ClockWorkKid/WiFi-Nano-Quadcopter/Quadcopter CAD Models/65mm-prop-1.snapshot.1/06.png

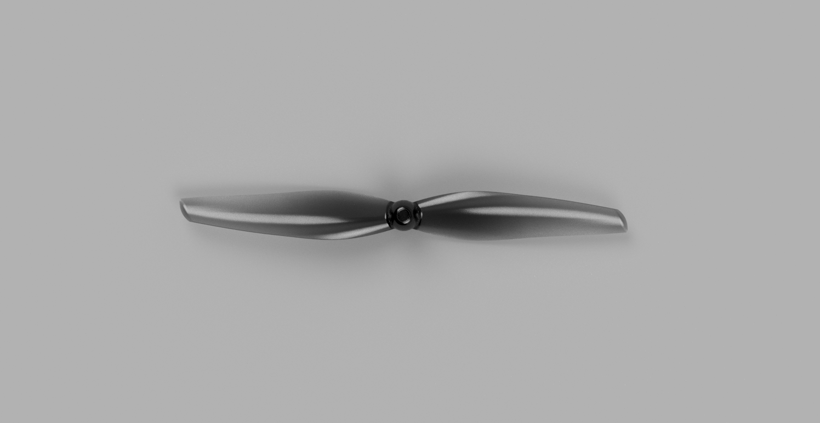
Quadcopter CAD Models/65mm-prop-1.snapshot.1/06.png
