ClockWorkKid/WiFi-Nano-Quadcopter/Quadcopter CAD Models/Micro_105_FPV_Quadcopter_-_8.5mm_Motors_Micro_Scisky/images/0fb575de4e6bde61108f173f8af68898_preview_featured.jpg

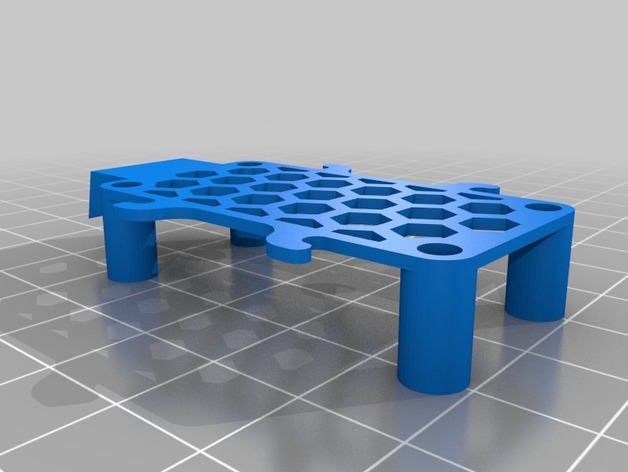
Quadcopter CAD Models/Micro_105_FPV_Quadcopter_-_8.5mm_Motors_Micro_Scisky/images/0fb575de4e6bde61108f173f8af68898_preview_featured.jpg
