ClockWorkKid/WiFi-Nano-Quadcopter/Quadcopter CAD Models/Micro_105_FPV_Quadcopter_-_8.5mm_Motors_Micro_Scisky/images/6a48a7edb29f2dee5ecd6720a6caf826_preview_featured.jpg

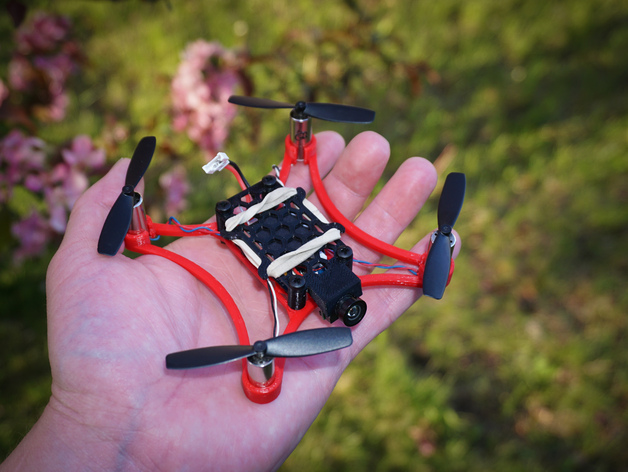
Quadcopter CAD Models/Micro_105_FPV_Quadcopter_-_8.5mm_Motors_Micro_Scisky/images/6a48a7edb29f2dee5ecd6720a6caf826_preview_featured.jpg
