ClockWorkKid/WiFi-Nano-Quadcopter/Quadcopter CAD Models/Micro_105_FPV_Quadcopter_-_8.5mm_Motors_Micro_Scisky/images/8fe7323692de997f5eb6b96ab5407ec9_preview_featured.jpg

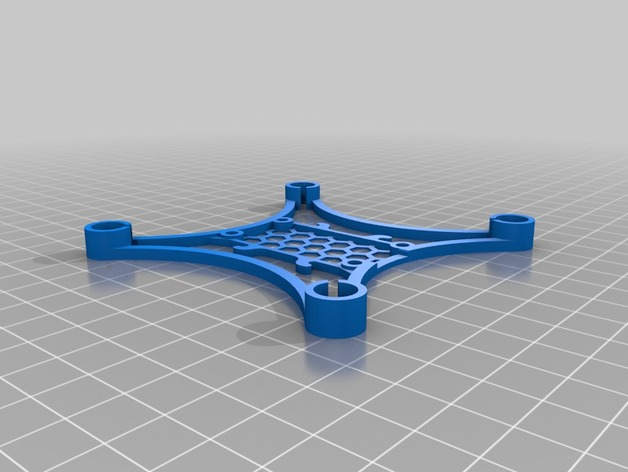
Quadcopter CAD Models/Micro_105_FPV_Quadcopter_-_8.5mm_Motors_Micro_Scisky/images/8fe7323692de997f5eb6b96ab5407ec9_preview_featured.jpg
