ClockWorkKid/WiFi-Nano-Quadcopter/Quadcopter CAD Models/Micro_105_FPV_Quadcopter_-_8.5mm_Motors_Micro_Scisky/images/84fe873a652a19607980b344e2987434_preview_featured.jpg

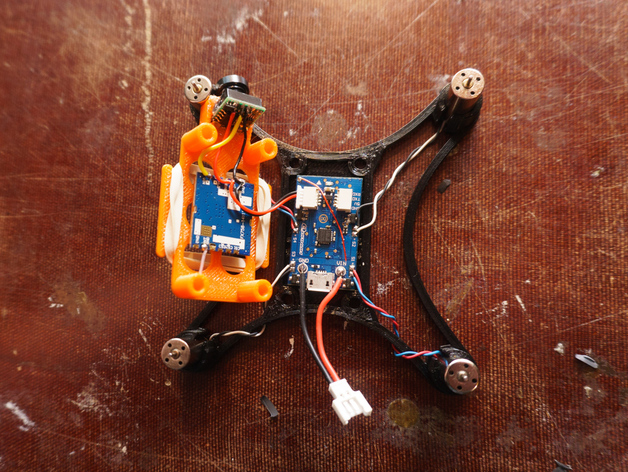
Quadcopter CAD Models/Micro_105_FPV_Quadcopter_-_8.5mm_Motors_Micro_Scisky/images/84fe873a652a19607980b344e2987434_preview_featured.jpg
