ClockWorkKid/WiFi-Nano-Quadcopter/Quadcopter CAD Models/Micro_105_FPV_Quadcopter_-_8.5mm_Motors_Micro_Scisky/images/832be2155cdcdc327818c795284aadd3_preview_featured.jpg

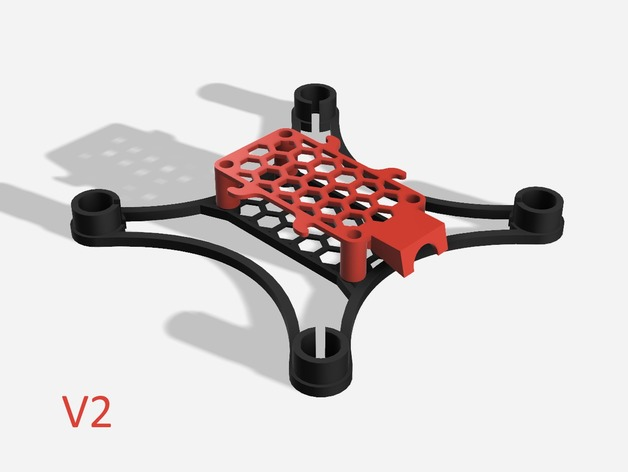
Quadcopter CAD Models/Micro_105_FPV_Quadcopter_-_8.5mm_Motors_Micro_Scisky/images/832be2155cdcdc327818c795284aadd3_preview_featured.jpg
