ClockWorkKid/WiFi-Nano-Quadcopter/Quadcopter CAD Models/Ryze_Tello_Propellers/images/2cdfefd59b9e02c92c9f1799bc0e8fc2_preview_featured.jpg

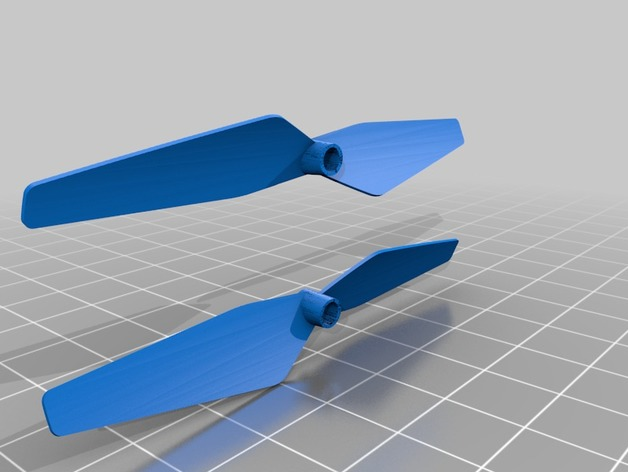
Quadcopter CAD Models/Ryze_Tello_Propellers/images/2cdfefd59b9e02c92c9f1799bc0e8fc2_preview_featured.jpg
