ClockWorkKid/WiFi-Nano-Quadcopter/Quadcopter CAD Models/Ryze_Tello_Propellers/images/3993e07cd14e0140e9b3e32e3a5cb526_preview_featured.jpg

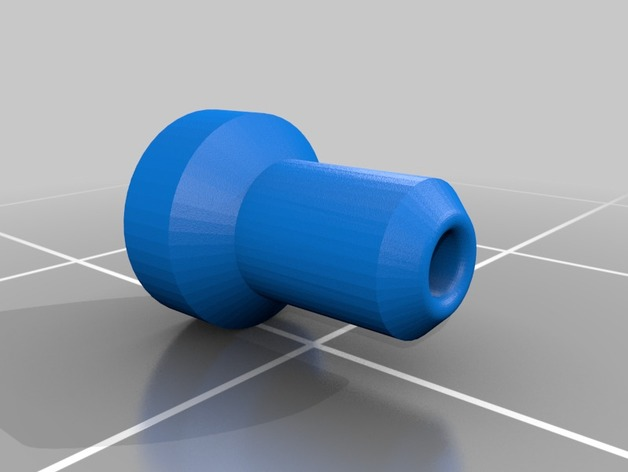
Quadcopter CAD Models/Ryze_Tello_Propellers/images/3993e07cd14e0140e9b3e32e3a5cb526_preview_featured.jpg
