ClockWorkKid/WiFi-Nano-Quadcopter/Quadcopter CAD Models/Ryze_Tello_Propellers/images/fef2fb93c76f4957c0f6beac872d470d_preview_featured.jpg

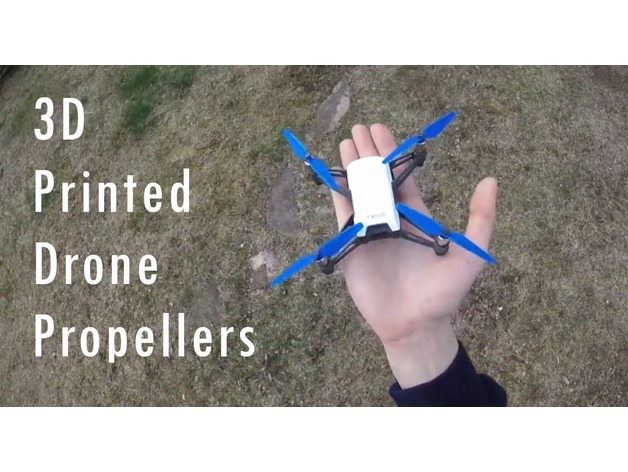
Quadcopter CAD Models/Ryze_Tello_Propellers/images/fef2fb93c76f4957c0f6beac872d470d_preview_featured.jpg
