ClockWorkKid/WiFi-Nano-Quadcopter/Quadcopter CAD Models/Micro_105_FPV_Quadcopter_-_8.5mm_Motors_Micro_Scisky/files/micro105-bottom-v4-bottom-battery.stl

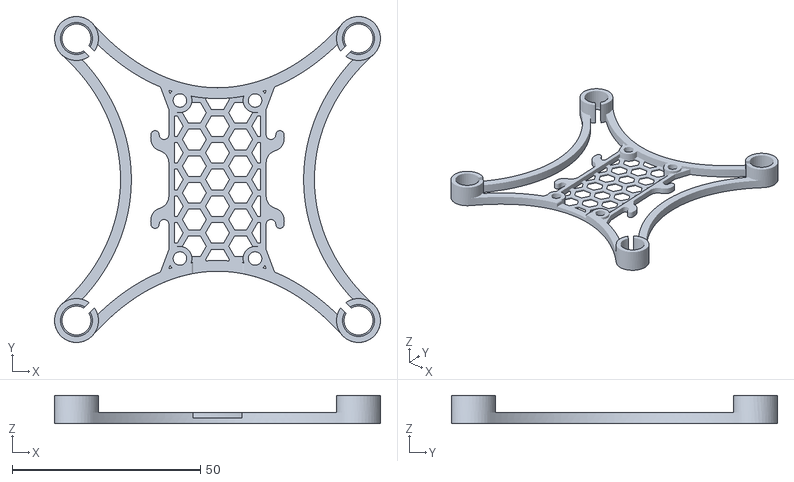
[picture p39: CAD file, 2020-05-22]
Quadcopter CAD Models/Micro_105_FPV_Quadcopter_-_8.5mm_Motors_Micro_Scisky/files/micro105-bottom-v4-bottom-battery.stl
86.7 x 86.7 x 7.50
