ClockWorkKid/WiFi-Nano-Quadcopter/Quadcopter CAD Models/Tello-STL-Files/Coreless_Motor.SLDPRT

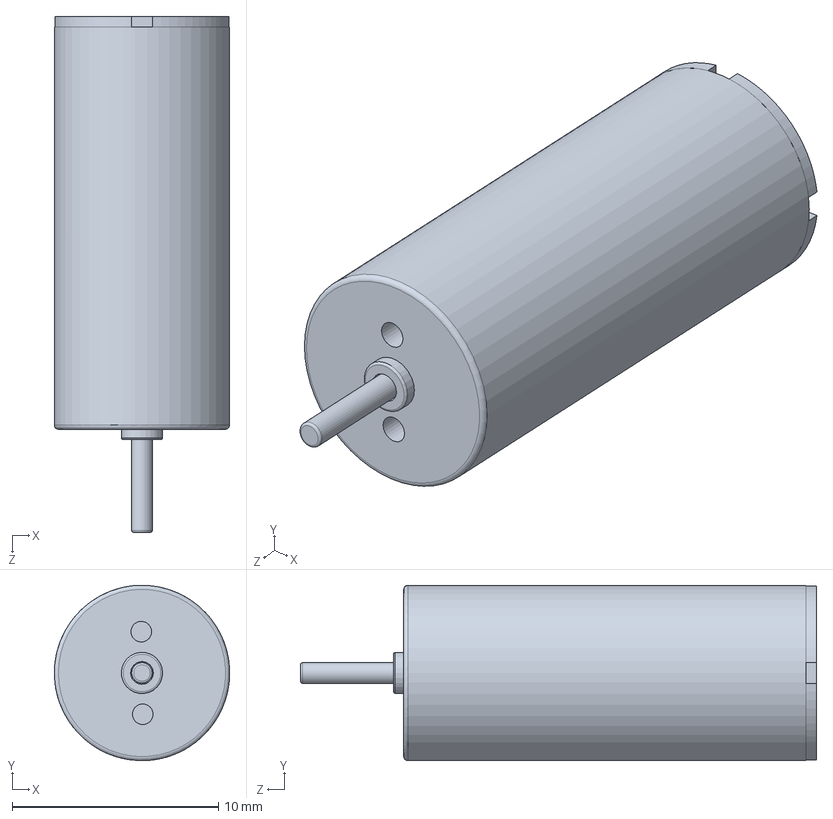
[picture p40: CAD file, 2020-05-22]
Quadcopter CAD Models/Tello-STL-Files/Coreless_Motor.SLDPRT
8.50 x 8.49 x 25.0 mm
