ClockWorkKid/WiFi-Nano-Quadcopter/Quadcopter CAD Models/Micro_105_FPV_Quadcopter_-_8.5mm_Motors_Micro_Scisky/files/micro105-top-v2-no-cam.stl

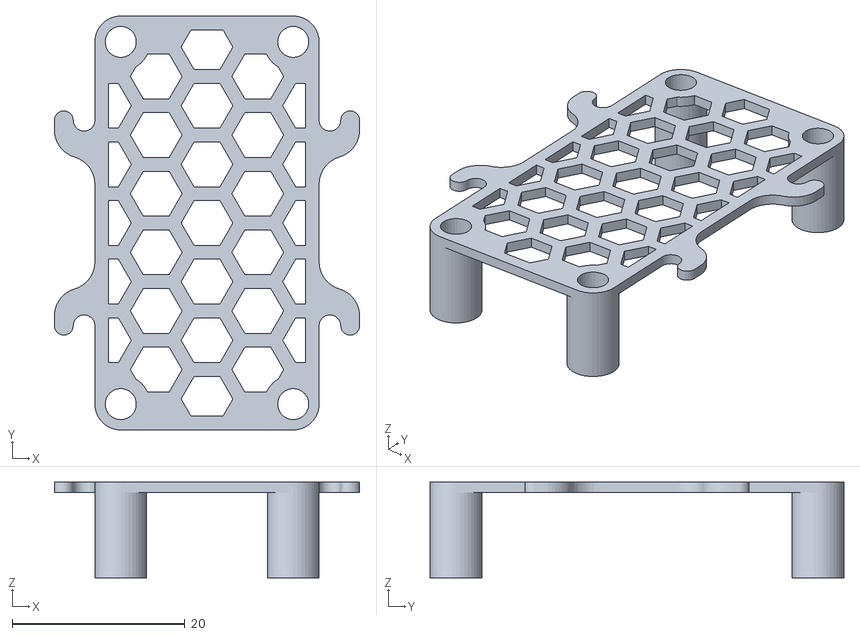
[picture p41: CAD file, 2020-05-22]
Quadcopter CAD Models/Micro_105_FPV_Quadcopter_-_8.5mm_Motors_Micro_Scisky/files/micro105-top-v2-no-cam.stl
35.4 x 48.0 x 11.1
