ClockWorkKid/WiFi-Nano-Quadcopter/Quadcopter CAD Models/Micro_105_FPV_Quadcopter_-_8.5mm_Motors_Micro_Scisky/files/micro105-top-v1.stl

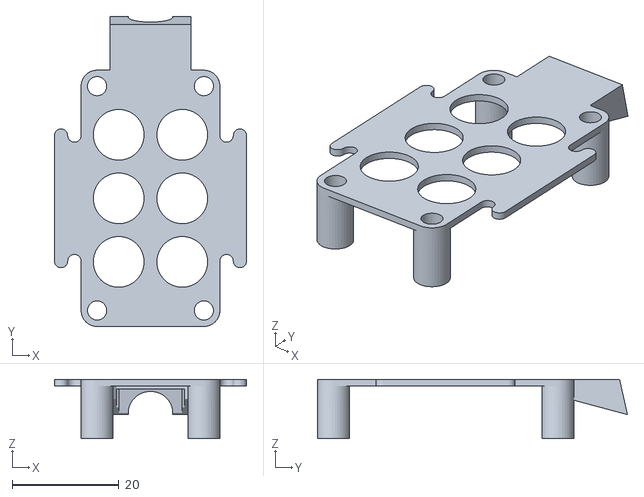
[picture p43: CAD file, 2020-05-22]
Quadcopter CAD Models/Micro_105_FPV_Quadcopter_-_8.5mm_Motors_Micro_Scisky/files/micro105-top-v1.stl
36.0 x 58.0 x 11.1
