ClockWorkKid/WiFi-Nano-Quadcopter/Quadcopter CAD Models/Micro_105_FPV_Quadcopter_-_8.5mm_Motors_Micro_Scisky/files/micro105-bottom-v4-7mm-bottom-battery.stl

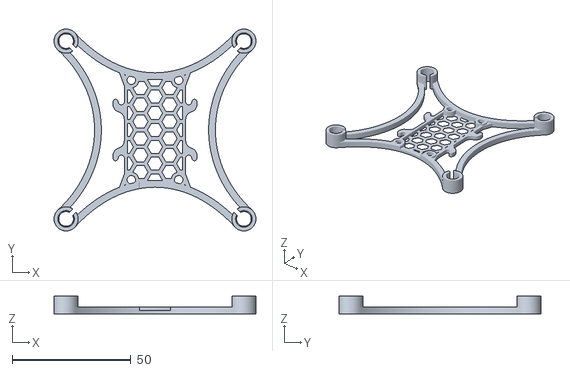
[picture p44: CAD file, 2020-05-22]
Quadcopter CAD Models/Micro_105_FPV_Quadcopter_-_8.5mm_Motors_Micro_Scisky/files/micro105-bottom-v4-7mm-bottom-battery.stl
85.2 x 85.2 x 7.50
