ClockWorkKid/WiFi-Nano-Quadcopter/Tests/Build 0/NodeMCU_V2_v2.png

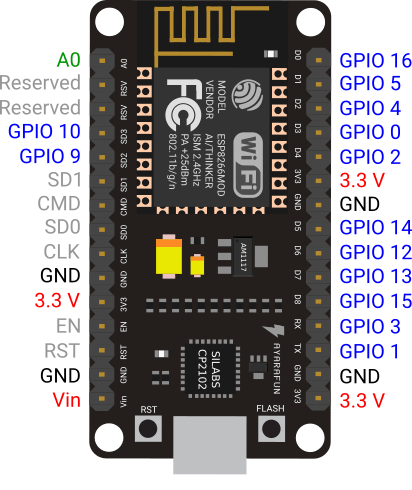
Tests/Build 0/NodeMCU_V2_v2.png
