ClockWorkKid/WiFi-Nano-Quadcopter/Tests/ESP-Quadcopter-Codes/ESPCOPTER_original/ESPcopter 1.0.3_2 BETA/espcopter/examples/Espcopter/Espcopter/data/media/info.png

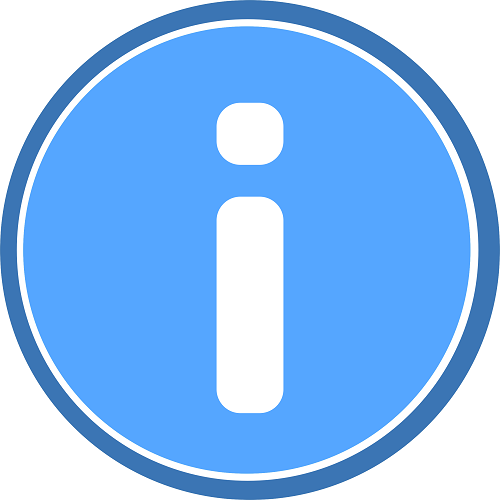
Tests/ESP-Quadcopter-Codes/ESPCOPTER_original/ESPcopter 1.0.3_2 BETA/espcopter/examples/Espcopter/Espcopter/data/media/info.png
