ClockWorkKid/WiFi-Nano-Quadcopter/Tests/ESP-Quadcopter-Codes/ESPCOPTER_original/ESPcopter 1.0.3_2 BETA/espcopter/examples/modules/alttidueHold/GetData/GetData.ino

/*
 * www.espcopter.com/learn
 * 
*/
#define standalone

#include <espcopter.h> // ESPcopter kütüphanesi


void setup() {
  mainSetup(); // uçuş ayarları
 }

void loop() {
   mainLoop ();  // uçuş kontrol döngüsü
   Serial.print("Yukseklik: ");
   Serial.print(getMeasureAltitude());
   Serial.println("mm");
}
