ClockWorkKid/WiFi-Nano-Quadcopter/Tests/ESP-Quadcopter-Codes/ESPCOPTER_original/ESPcopter 1.0.3_2 BETA/espcopter/examples/modules/buzzer/HappyBirthDay/HappyBirthDay.ino

/*
 * www.espcopter.com/learn
 * 
*/
// * Happy Birthday to You

int length = 28; 
char notes[] = "GGAGcB GGAGdc GGxecBA yyecdc";
int beats[] = { 2, 2, 8, 8, 8, 16, 1, 2, 2, 8, 8,8, 16, 1, 2,2,8,8,8,8,16, 1,2,2,8,8,8,16 };
int tempo = 150;

void playTone(int tone, int duration) {
for (long i = 0; i < duration * 1000L; i += tone * 2) {
 analogWrite(2, 0);
 analogWrite(12, 40);
 analogWrite(13, 40);
 analogWrite(14, 40);
 analogWrite(15, 40);    
 delayMicroseconds(tone);
 analogWrite(2, 1023);
 analogWrite(12, 0);
 analogWrite(13, 0);
 analogWrite(14, 0);
 analogWrite(15, 0);
 delayMicroseconds(tone);
}
}

void playNote(char note, int duration) {

char names[] = {'C', 'D', 'E', 'F', 'G', 'A', 'B',           

                 'c', 'd', 'e', 'f', 'g', 'a', 'b',

                 'x', 'y' };

int tones[] = { 1915, 1700, 1519, 1432, 1275, 1136, 1014,

                 956,  834,  765,  593,  468,  346,  224,

                 655 , 715 };

int SPEE = 5;
// play the tone corresponding to the note name
for (int i = 0; i < 17; i++) {
   if (names[i] == note) {
    int newduration = duration/SPEE;
     playTone(tones[i], newduration);

   }
}
}

void setup() {
pinMode(2, OUTPUT);
}

void loop() {
for (int i = 0; i < length; i++) {
   if (notes[i] == ' ') {
     delay(beats[i] * tempo); // rest
   } else {
     playNote(notes[i], beats[i] * tempo);
   }
 analogWrite(16, 1000);
   // pause between notes
   delay(tempo);
 analogWrite(16, 0);
}
}
