ClockWorkKid/WiFi-Nano-Quadcopter/Tests/Codes-Test/SONAR/IR_Receiver/interrupt_recv.ino

//int counter = 0;
//
//#define sync1 4 //D2
////#define sync1 5 //D1
//
//void setup() {
//  Serial.begin(115200);
//  attachInterrupt(digitalPinToInterrupt(sync1), pulseCB, FALLING);
//}
//
//ICACHE_RAM_ATTR void pulseCB() {
//  counter++;
//  Serial.println(counter);
//}
//
//
//void loop() {
//
//}
