ClockWorkKid/WiFi-Nano-Quadcopter/Tests/Codes-Test/SONAR/IR_Receiver/remote_recv.ino

#include <Arduino.h>
#include <IRremoteESP8266.h>
#include <IRrecv.h>
#include <IRutils.h>

// An IR detector/demodulator is connected to GPIO pin 14(D5 on a NodeMCU
// board).
// Note: GPIO 16 won't work on the ESP8266 as it does not have interrupts.
const uint16_t kRecvPin = 14;

IRrecv irrecv(kRecvPin);

decode_results results;

void setup() {
  Serial.begin(115200);
  irrecv.enableIRIn();  // Start the receiver

  Serial.println();
  Serial.print("IRrecvDemo is now running and waiting for IR message on Pin ");
  Serial.println(kRecvPin);
}

unsigned long counter=0;

void loop() {
  if (irrecv.decode(&results)) {
    Serial.print(counter++);
    Serial.print(" ");
    serialPrintUint64(results.value);
    Serial.println("");
    irrecv.resume();  // Receive the next value
  }
}
