ClockWorkKid/WiFi-Nano-Quadcopter/Tests/Codes-Test/SONAR/IR_Transmitter/remote_tran.ino

/*
 * IRremote: IRsendDemo - demonstrates sending IR codes with IRsend
 * An IR LED must be connected to Arduino PWM pin 3.
 * Version 0.1 July, 2009
 * Copyright 2009 Ken Shirriff
 * http://arcfn.com
 */

#include <IRremote.h>

IRsend IrSender;

// On the Zero and others we switch explicitly to SerialUSB
#if defined(ARDUINO_ARCH_SAMD)
#define Serial SerialUSB
#endif

void setup() {
    pinMode(LED_BUILTIN, OUTPUT);

    Serial.begin(115200);
#if defined(__AVR_ATmega32U4__) || defined(SERIAL_USB) || defined(SERIAL_PORT_USBVIRTUAL)
    delay(2000); // To be able to connect Serial monitor after reset and before first printout
#endif
    // Just to know which program is running on my Arduino
    Serial.println(F("START " __FILE__ " from " __DATE__));
    Serial.print(F("Ready to send IR signals at pin "));
    Serial.println(IR_SEND_PIN);
}

unsigned long counter=0;

void loop() {
    unsigned long tData = 0xb91;
    IrSender.sendSony(tData, 12);
    Serial.print(counter++);
    Serial.print(" ");
    Serial.println(tData);
//        IrSender.sendJVC(0xC5B8, 16,0); // hex value, 16 bits, no repeat
//        delayMicroseconds(50); // see http://www.sbprojects.com/knowledge/ir/jvc.php for information
//        IrSender.sendJVC(0xC5B8, 16,1); // hex value, 16 bits, repeat
//        Serial.println(F("sendJVC(9xC5B8, 16)"));

    delay(1000); //5 second delay between each signal burst
}
