ClockWorkKid/WiFi-Nano-Quadcopter/Tests/Codes-Test/SONAR/IR_Transmitter/timer.ino

//unsigned long timer = 0;
//bool state = 0;
//
//void setup() {
//  pinMode(13, OUTPUT);
//
//  TCCR0A = (1 << WGM01); //Set the CTC mode
//  OCR0A = 1;          //Value for ORC0A for 1ms
//
//  TIMSK0 |= (1 << OCIE0A); //Set the interrupt request
//  sei(); //Enable interrupt
//
//  TCCR0B |= (1 << CS01); //Set the prescale 1/64 clock
//  TCCR0B |= (1 << CS00);
//
//}
//
//void loop() {
//
//}
//
//ISR(TIMER0_COMPA_vect) {   //This is the interrupt request
//  timer++;
//  //in this way you can count 1 second because the nterrupt request is each 1ms
//  if (timer >= 125000) {
//    state = !state;
//    timer = 0;
//    digitalWrite(13, state);
//  }
//
//}
