ClockWorkKid/WiFi-Nano-Quadcopter/Tests/ESP-Quadcopter-Codes/ESPCOPTER_original/ESPcopter 1.0.3_2 BETA/espcopter/src/AHRS.cpp

#include "AHRS.h"
#include <Wire.h>


int previousDegree;
 float angle=0;
 float heading=0;


String AHRS::setupOutput(){

  String ahrsOutput= "";
  
  ahrsOutput = ahrsOutput + "-----------------------------"  + '\n';
  ahrsOutput = ahrsOutput + "Calibration Data:"  + '\n';
  ahrsOutput = ahrsOutput + "Magnometer Motor Calibraiton: " + '\n';
  ahrsOutput = ahrsOutput + "MagX: "  ;
  ahrsOutput = ahrsOutput + magOffsetMotorEpr[0];
  ahrsOutput = ahrsOutput +" MagY: ";
  ahrsOutput = ahrsOutput + magOffsetMotorEpr[1] + '\n';
      
  ahrsOutput = ahrsOutput + "-----------------------------"  + '\n';
  ahrsOutput = ahrsOutput + "Magnometer Calibraiton: "  + '\n';
  ahrsOutput = ahrsOutput + "Offx: ";
  ahrsOutput = ahrsOutput + magOffset[0];
  ahrsOutput = ahrsOutput + " Offy: ";
  ahrsOutput = ahrsOutput + magOffset[1];
  ahrsOutput = ahrsOutput + " Offz: ";
  ahrsOutput = ahrsOutput + magOffset[2] + '\n';

  ahrsOutput = ahrsOutput + "-----------------------------"  + '\n';
  ahrsOutput = ahrsOutput + "GYRO Calibration: "  + '\n'; 
  ahrsOutput = ahrsOutput + "GYROX: ";
  ahrsOutput = ahrsOutput + MEAN_GYRO[0];
  ahrsOutput = ahrsOutput + " GYROY: ";
  ahrsOutput = ahrsOutput + MEAN_GYRO[1];
  ahrsOutput = ahrsOutput + " GYROZ: ";
  ahrsOutput = ahrsOutput + MEAN_GYRO[2] + '\n';

  I2Cread(MPU9250_ADDRESS,0x3B,14,Buf);
  accel[0]=(Buf[0]<<8 | Buf[1]) - MEAN_ACCE[0]; 
  accel[1]=(Buf[2]<<8 | Buf[3]) - MEAN_ACCE[1]; 
  accel[2]=(Buf[4]<<8 | Buf[5]) - MEAN_ACCE[2];
 
  // Gyroscope
  gyro_int[0]=(Buf[8]<<8 | Buf[9]) - MEAN_GYRO[0];
  gyro_int[1]=(Buf[10]<<8 | Buf[11]) - MEAN_GYRO[1];
  gyro_int[2]=Buf[12]<<8 | Buf[13] - MEAN_GYRO[2];


  ahrsOutput = ahrsOutput + "-----------------------------"  + '\n';
  ahrsOutput = ahrsOutput + "GYRO Data: "  + '\n'; 
  ahrsOutput = ahrsOutput + "GYRO_Roll: ";
  ahrsOutput = ahrsOutput + gyro_int[0];
  ahrsOutput = ahrsOutput + " GYRO_Pitch: ";
  ahrsOutput = ahrsOutput + gyro_int[1];
  ahrsOutput = ahrsOutput + " GYRO_Yaw: ";
  ahrsOutput = ahrsOutput + gyro_int[2] + '\n';

   
  ahrsOutput = ahrsOutput + "-----------------------------"  + '\n';
  ahrsOutput = ahrsOutput + "IMU Calibration: "  + '\n'; 
  ahrsOutput = ahrsOutput + "IMU_Roll: ";
  ahrsOutput = ahrsOutput + MEAN_ACCE[0];
  ahrsOutput = ahrsOutput + " IMU_Pitch: ";
  ahrsOutput = ahrsOutput + MEAN_ACCE[1] ;
  ahrsOutput = ahrsOutput + " IMU_Yaw: ";
  ahrsOutput = ahrsOutput + MEAN_ACCE[2] + '\n';
     


  ahrsOutput = ahrsOutput + "-----------------------------"  + '\n';
  ahrsOutput = ahrsOutput + "IMU Data: "  + '\n'; 
  ahrsOutput = ahrsOutput + "IMU_Roll: ";
  ahrsOutput = ahrsOutput + accel[0];
  ahrsOutput = ahrsOutput + " IMU_Pitch: ";
  ahrsOutput = ahrsOutput + accel[1];
  ahrsOutput = ahrsOutput + " IMU_Yaw: ";
  ahrsOutput = ahrsOutput + accel[2] + '\n';

 // Serial.print(ahrsOutput);
  return ahrsOutput;
}


void AHRS::calibraiton(int calMethod){
  
    Serial.print(" calMethod");
    Serial.println(calMethod);

    
   if( calMethod == 0){
   digitalWrite(redLed, 1); //  0 == 1 
   digitalWrite(greenLed, 0); // 0 == 0 
   digitalWrite(blueLed, 0); //  0 == 1

   Serial.println(" Gyro Calibration Progress Started");
   gyroCorrection(2000);

   Serial.println(" Accel Calibration Progress Started");
   accelCorrection(2000);

   digitalWrite(redLed, 1); //  0 == 1 
   digitalWrite(greenLed, 1); // 0 == 0 
   digitalWrite(blueLed, 1); //  0 == 1
   }


   if( calMethod == 1){
   digitalWrite(redLed, 1); //  0 == 1 
   digitalWrite(greenLed, 0); // 0 == 0 
   digitalWrite(blueLed, 0); //  0 == 1

   Serial.println(" Mag Calibration Progress Started");
   analogWriteFreq(20000);
   magCalStage = 1;
   magCorrection(1000);
   magCalStage =0;
   
   digitalWrite(redLed, 1); //  0 == 1 
   digitalWrite(greenLed, 1); // 0 == 0 
   digitalWrite(blueLed, 1); //  0 == 1
   }
   
   if( calMethod == 2){
  
   }
    

   

   EEPROM.write(25,highByte(0)); // aotu set 
   EEPROM.write(26,lowByte(0));
   /*
   EEPROM.write(35,highByte(0));
   EEPROM.write(36,lowByte(0));  // optical

   EEPROM.write(37,highByte(0));
   EEPROM.write(38,lowByte(0));*/                                                                

   EEPROM.write(42,highByte(0)); // yaw
   EEPROM.write(43,lowByte(0));
   
   
  EEPROM.commit();

  if( calMethod == 1){
  delay(100);
  ESP.restart();
   }
   
  
}


 
void AHRS::Initialize(){
  // Start I2C Communication
  //Wire.begin();
  Wire.setClock(400000L);
  //Wire.setClockStretchLimit(500L);
  
  // Set accelerometers low pass filter at 5Hz
  writeBIT(29, 0x06,MPU9250_ADDRESS);
  // Set gyroscope low pass filter at 5Hz
  writeBIT(26, 0x06,MPU9250_ADDRESS);
  // Configure gyroscope range
  writeBIT(27, GYRO_FULL_SCALE_2000_DPS,MPU9250_ADDRESS);
  // Configure accelerometers range
  writeBIT(28, ACC_FULL_SCALE_2_G,MPU9250_ADDRESS);
  // Set by pass mode for the magnetometers
  writeBIT(0x37, 0x02,MPU9250_ADDRESS);
  // Request continuous magnetometer measurements in 16 bits
  //writeBIT(0x0A, 0x16,MAG_ADDRESS);
   delay(20);

  writeBIT(0x0A, 0x00 , MAG_ADDRESS); // Power down magnetometer  
  delay(20);
  writeBIT(0x0A  , 0x0F, MAG_ADDRESS); // Enter Fuse ROM access mode
  delay(20);
  uint8_t rawData[3];
  I2Cread(MAG_ADDRESS,0x10,3,rawData);
  destination[0] =  (float)(rawData[0] - 128)/256. + 1.;   // Return x-axis sensitivity adjustment values, etc.
  destination[1] =  (float)(rawData[1] - 128)/256. + 1.;  
  destination[2] =  (float)(rawData[2] - 128)/256. + 1.; //28 , 238 , 254 , 0.61 , 1.43 , 1.49

   Serial.print("Sensitivity: ");
   Serial.print(destination[0]);
   Serial.print(" , ");
   Serial.print(destination[1]);
   Serial.print(" , ");
   Serial.println(destination[2]);
   delay(20);
   
   writeBIT(0x0A, 0x00, MAG_ADDRESS); // Power down magnetometer  
   delay(20);
   // Configure the magnetometer for continuous read and highest resolution
   // set Mscale bit 4 to 1 (0) to enable 16 (14) bit resolution in CNTL register,
   // and enable continuous mode data acquisition Mmode (bits [3:0]), 0010 for 8 Hz and 0110 for 100 Hz sample rates
   writeBIT(0x0A, Mscale << 4 | Mmode,MAG_ADDRESS); // Set magnetometer data resolution and sample ODR
   delay(20);
 
  
  
   Serial.print("Read Eeprom...");


   MEAN_GYRO[0] = word(EEPROM.read(1),EEPROM.read(2));
   MEAN_GYRO[1] = word(EEPROM.read(3),EEPROM.read(4));
   MEAN_GYRO[2] = word(EEPROM.read(5),EEPROM.read(6));


   MEAN_ACCE[0] = word(EEPROM.read(70),EEPROM.read(71));
   MEAN_ACCE[1] = word(EEPROM.read(72),EEPROM.read(73));
   MEAN_ACCE[2] = word(EEPROM.read(74),EEPROM.read(75));

   magOffset[0] = word(EEPROM.read(10),EEPROM.read(11));
   magOffset[1] = word(EEPROM.read(20),EEPROM.read(21));
   magOffset[2] = word(EEPROM.read(30),EEPROM.read(31));

   magOffsetMotorEpr[0] = word(EEPROM.read(40),EEPROM.read(41));
   magOffsetMotorEpr[1] = word(EEPROM.read(50),EEPROM.read(51));
 
   magOffsetMotorEpr[2] = word(EEPROM.read(45),EEPROM.read(46));
   magOffsetMotorEpr[3] = word(EEPROM.read(55),EEPROM.read(56));

  // destination2[0] = word(EEPROM.read(12),EEPROM.read(13))/100;
  // destination2[1] = word(EEPROM.read(14),EEPROM.read(15))/100;



    
  Serial.print(" destination20: ");
  Serial.print(destination2[0]);
  Serial.print(" destination21: ");
  Serial.print(destination2[1]);
  Serial.print(" MagX: ");
  Serial.print(magOffsetMotorEpr[0]);
  Serial.print(" MagY: ");
  Serial.print(magOffsetMotorEpr[1]);
  Serial.print(" Offx: ");
  Serial.print(magOffset[0]);
  Serial.print(" Offy: ");
  Serial.print(magOffset[1]);
  Serial.print(" Offz:");
  Serial.print(magOffset[2]);  
  Serial.print(" GYROX: "); 
  Serial.print(MEAN_GYRO[0]);
  Serial.print(" GYROY: ");
  Serial.print(MEAN_GYRO[1]);
  Serial.print(" GYROZ: ");
  Serial.println(MEAN_GYRO[2]);
}

void AHRS::writeBIT(int addr, int data, int adrrTrans){
  Wire.beginTransmission(adrrTrans);
  Wire.write(addr);
  Wire.write(data);
  Wire.endTransmission();
}
void AHRS::I2Cread(uint8_t Address, uint8_t Register, uint8_t Nbytes, uint8_t* Data){
// Set register address
Wire.beginTransmission(Address);
Wire.write(Register);
Wire.endTransmission();
// Read Nbytes
Wire.requestFrom(Address, Nbytes); 
uint8_t index=0;
while (Wire.available())
Data[index++]=Wire.read();
}

float AHRS::rad2deg(float rad){
  float output = rad * (180.0 / PI);
  return output;
}

float AHRS::deg2rad(float deg){
  float output = deg * (PI / 180.0);
  return output;
}

void AHRS::setTrimRoll(int16_t trimRoll_){
   trimRoll =  trimRoll_;
}
void AHRS::setTrimPitch(int16_t trimPitch_){
   trimPitch =  trimPitch_;
}

float AHRS::getAccelX(){
  return accel[0];
}

float AHRS::getAccelY(){
  return accel[1];
}

float AHRS::getAccelZ(){
  return accel[2];
}

float AHRS::getGyroX(){
  return gyro_int[0];
}

float AHRS::getGyroY(){
  return gyro_int[1];
}
float AHRS::getGyroZ(){
  return gyro_int[2];
}

void AHRS::compute(float attitude[3], float rate[3],float attitudeRadian[3], float rateRadian[3] ){
    timenow = millis();
    dt = (float)(timenow - timeprev)/978.;
    timeprev = timenow;

    if(dt > -1){
        
    // Get Raw Data From IMU
    I2Cread(MPU9250_ADDRESS,0x3B,14,Buf);
    accel[0]=(Buf[0]<<8 | Buf[1]) - MEAN_ACCE[0]; //-520
    accel[1]=(Buf[2]<<8 | Buf[3]) - MEAN_ACCE[1]; //-300
    accel[2]=(Buf[4]<<8 | Buf[5]) - MEAN_ACCE[2];
 
    // Gyroscope
    gyro_int[0]=(Buf[8]<<8 | Buf[9]) - MEAN_GYRO[0];
    gyro_int[1]=(Buf[10]<<8 | Buf[11]) - MEAN_GYRO[1];
    gyro_int[2]=Buf[12]<<8 | Buf[13] - MEAN_GYRO[2];

 /*
    Serial.print( gyro_int[0] );
    Serial.print(" , ");
    Serial.print( gyro_int[1] );
    Serial.print(" , ");
    Serial.print( gyro_int[2] );
    Serial.print(" , ");
    Serial.print( accel[0] );
    Serial.print(" , ");
    Serial.print( accel[1] );
    Serial.print(" , ");
    Serial.print( accel[2] );
    Serial.println(); */

      
    // Get Gyro 
    for(i = 0; i<3 ; i++){
    gyro[i] = (gyro_int[i] / GYRO_LSB)*DEG2RAD;
    }   
  
    // Normalize Accelerometer
    normalize(accel_angle, accel);
    
   // Calculate deltaAngle
    gyro_angle_x = gyro_angle_x + (gyro_angle_y* gyro[2] - gyro_angle_z* gyro[1])*dt;
    gyro_angle_y = gyro_angle_y + (gyro_angle_z* gyro[0] - gyro_angle_x* gyro[2])*dt;
    gyro_angle_z = gyro_angle_z + (gyro_angle_z* gyro[1] - gyro_angle_y* gyro[0])*dt;


    // Apply Complementary Filter
    // Apply when |a| - 1 < 0.10 to eliminate other forces
    
    if((abs(norm)/16384.) - 1 <= 0.15) {//0.15
     gyro_angle_x = A_A* gyro_angle_x + (1 - A_A) *  accel_angle[0];
     gyro_angle_y = A_A* gyro_angle_y + (1 - A_A) *  accel_angle[1];
     gyro_angle_z = A_A* gyro_angle_z + (1 - A_A) *  accel_angle[2];
    }


    // Convert
    attitude[0] = atan2(gyro_angle_y, sqrt(gyro_angle_x*gyro_angle_x + gyro_angle_z*gyro_angle_z)); // ROLL
    attitude[1] = atan2(gyro_angle_x, gyro_angle_z); // PITCH
   
  
    // Calculate Euler Rates
    rate[0] =  (gyro[0] + ( attitude[1] * attitude[0] * attitude[1]) + ( gyro[2] * (1 - (attitude[0]*attitude[0]) / 2) * attitude[1]));
    rate[1] =  (gyro[1] * (1 - ((attitude[0]*attitude[0])/2)) -  gyro[2] * attitude[0]);  
    rate[2] = gyro[2];

    rateRadian[0] =  rate[0];
    rateRadian[1] =  rate[1];
    rateRadian[2] =  rate[2];

    rate[0] =  rate[0]*100*RAD2DEG;
    rate[1] =  rate[1]*100*RAD2DEG;
    rate[2] =  rate[2]*100*RAD2DEG;

    
    float alpha = 0.85;
    for(i = 0; i<3 ; i++){
    rate[i] = (alpha*(float)rate[i]) + ((1-alpha)*(float)_rate[i]);
   _rate[i] = rate[i];
   }

  attitudeRadian[0] =  attitude[0];
  attitudeRadian[1] =  attitude[1];

  attitude[0] *= 100*RAD2DEG;
  attitude[1] *= 100*RAD2DEG;
  /*
  float alpha2 = 0.95;//95
   for(i = 0; i<2 ; i++){
    attitude[i] = (alpha2*(float)attitude[i]) + ((1-alpha2)*(float)_attitude[i]);
   _attitude[i] = attitude[i];
  } */
  
  }else{
  Serial.print((float)dt);
  Serial.println("Eror AHRS");
  }
}

void AHRS::normalize(float output[3], int16_t input[3]){
  norm = sqrt(input[0]* input[0] + input[1]*input[1] + input[2]* input[2]);
  output[0] = input[0] / (float)norm;
  output[1] = input[1] / (float)norm;
  output[2] = input[2] / (float)norm;
}
void AHRS::setZero()
{
 gyro_angle_x =0;
 gyro_angle_y =0;
 gyro_angle_z =0;
}

int16_t  AHRS::readTemp(){
 uint8_t rawData[2];  // x/y/z gyro register data stored here
  I2Cread(MPU9250_ADDRESS, 0x41, 2, &rawData[0]);  // Read the two raw data registers sequentially into data array 
  return ((int16_t)rawData[0] << 8) | rawData[1] ;  // Turn the MSB and LSB into a 16-bit value
}



void AHRS::gyroCorrection(uint16_t itinary){

  SUM_GYRO[0] = 0;
  SUM_GYRO[1] = 0;
  SUM_GYRO[2] = 0;
  
    for(i=0;i<itinary;i++){
     I2Cread(MPU9250_ADDRESS,0x3B,14,Buf);
     gyro_intCal[0]=(Buf[8]<<8 | Buf[9]);
     gyro_intCal[1]=(Buf[10]<<8 | Buf[11]);
     gyro_intCal[2]=Buf[12]<<8 | Buf[13];
     SUM_GYRO[0] += gyro_intCal[0];
     SUM_GYRO[1] += gyro_intCal[1];
     SUM_GYRO[2] += gyro_intCal[2];
     delay(1);
    }

   MEAN_GYRO[0] = SUM_GYRO[0] / itinary;
   MEAN_GYRO[1] = SUM_GYRO[1] / itinary;
   MEAN_GYRO[2] = SUM_GYRO[2] / itinary;
     
   EEPROM.write(1,highByte(MEAN_GYRO[0]));
   EEPROM.write(2,lowByte(MEAN_GYRO[0]));

   EEPROM.write(3,highByte(MEAN_GYRO[1]));
   EEPROM.write(4,lowByte(MEAN_GYRO[1]));

   EEPROM.write(5,highByte(MEAN_GYRO[2]));
   EEPROM.write(6,lowByte(MEAN_GYRO[2]));

   Serial.print(MEAN_GYRO[0]);
   Serial.print("  ,  ");
   Serial.print(MEAN_GYRO[1]);
   Serial.print("  ,  ");
   Serial.println(MEAN_GYRO[2]);
   Serial.println(" GyroCorrection is Complated: ");
    
 }

void AHRS::accelCorrection(uint16_t itinary){
  
      SUM_ACCE[0] = 0; 
      SUM_ACCE[1] = 0; 
      SUM_ACCE[2] = 0; 
    
      for(i=0;i<itinary;i++){
      I2Cread(MPU9250_ADDRESS,0x3B,14,Buf); 
      accelCal[0]=(Buf[0]<<8 | Buf[1]); //-520
      accelCal[1]=(Buf[2]<<8 | Buf[3]); //-300
      accelCal[2]=(Buf[4]<<8 | Buf[5]); 

      SUM_ACCE[0] += accelCal[0];
      SUM_ACCE[1] += accelCal[1];
      SUM_ACCE[2] =  (16384 - accelCal[2]) + SUM_ACCE[2];
      delay(1);
      }


      MEAN_ACCE[0] = SUM_ACCE[0] / itinary;
      MEAN_ACCE[1] = SUM_ACCE[1] / itinary;
      MEAN_ACCE[2] = -SUM_ACCE[2] / itinary;

      
      EEPROM.write(70,highByte(MEAN_ACCE[0]));
      EEPROM.write(71,lowByte(MEAN_ACCE[0]));
 
      EEPROM.write(72,highByte(MEAN_ACCE[1]));
      EEPROM.write(73,lowByte(MEAN_ACCE[1]));

      EEPROM.write(74,highByte(MEAN_ACCE[2]));
      EEPROM.write(75,lowByte(MEAN_ACCE[2]));

     
      Serial.print(MEAN_ACCE[0]);
      Serial.print("  ,  ");
      Serial.print(MEAN_ACCE[1]);
      Serial.print("  ,  ");
      Serial.println(MEAN_ACCE[2]);
      Serial.println(" Accel Correction is Complated: ");
      

 }


void AHRS::magCorrection(uint16_t itinary){
  magOffset[0]= 0;
  magOffset[1]= 0;
  magOffset[2]= 0;
  magOffsetMotorFnl[0]=0;
  magOffsetMotorFnl[1]=0;
  
  float attitudeFake[3] = {0};

  float  rateFake[3] = {0};
  float magOffsetMotorFnlFake[3] = {0};
  
 headingMag(rateFake,attitudeFake, degree ,0.0); 
  
  minX = degree[1];
  maxX = degree[1];
  minY = degree[2];
  maxY = degree[2];
  
  for(i=0;i<itinary;i++){  
  headingMag(rateFake,attitudeFake, degree , 0); 

  if (degree[1] < minX) minX = degree[1];
  if (degree[1] > maxX) maxX = degree[1];
  
  if (degree[2] < minY) minY = degree[2];
  if (degree[2] > maxY) maxY = degree[2];

  
    Serial.print("minX = ");
    Serial.print(minX);
    Serial.print("  ,  ");
    Serial.print(maxX);
    Serial.print("  ,  ");
    Serial.print(minY);
    Serial.print("  ,  ");
    Serial.print(maxY);
    Serial.print("  ,  ");
    Serial.print(degree[1]);
    Serial.print("  ,  ");
    Serial.print(degree[2]);
    Serial.print("  ,  ");
    Serial.println(degree[3]);
    delay(12);
    }
    
  analogWrite(redLed, 1);// red opened
  analogWrite(greenLed, 1);
  analogWrite(blueLed, 0); // Blue opened
   
   delay(1000);

   
   magOffset[0] = (maxX + minX)/2; 
   magOffset[1] = (maxY + minY)/2;

   mag_scale[0]  = (maxX - minX)/2;  // get average x axis max chord length in counts
   mag_scale[1]  = (maxY - minY)/2; // get average y axis max chord length in counts
    
   float avg_rad  = (mag_scale[0] + mag_scale[1])/2;
  

   destination2[0] = avg_rad/((float)mag_scale[0]) ;
   destination2[1] = avg_rad/((float)mag_scale[1]) ;

   
  
  Serial.print(" 1 offX: ");
  Serial.print(magOffset[0]);
  Serial.print(" 1 offY: ");
  Serial.print(magOffset[1]);
  Serial.print(" 1 offZ: ");
  Serial.println(magOffset[2]);  


  while(1){
    headingMag(rateFake,attitudeFake, degree , 0 ); 
    if( magOffsetMotorCount < 200 && degree_[2] != degree[2] &&degree_[1] != degree[1] ){
    magOffsetMotorCount += 1;
    magOffsetMotor[0] += degree[1];
    magOffsetMotor[1] += degree[2];
    degree_[1] = degree[1];
    degree_[2] = degree[2];
    Serial.print("degreeX = ");
    Serial.print(degree[1]);
    Serial.print(" degreeY = ");
    Serial.print(degree[2]);
    Serial.println();
    }else if( magOffsetMotorCount == 200){
    sumMagOffsetMotor[0] = magOffsetMotor[0]/200;
    sumMagOffsetMotor[1] = magOffsetMotor[1]/200;
    break;
    }
  }
    Serial.println();
    Serial.println("ORT = ");
    Serial.println();
    Serial.print("sumMagX = ");
    Serial.print(sumMagOffsetMotor[0]);
    Serial.print(" sumMagY = ");
    Serial.print(sumMagOffsetMotor[1]);
    Serial.println();
    
for(int i =0; i< 30; i++){
  analogWrite(14, i*10);
  analogWrite(15, i*10);
  analogWrite(12, i*10);
  analogWrite(13, i*10);
  delay(25);
}
   while(1){
    analogWrite(14, 700);
    analogWrite(15, 700);
    analogWrite(12, 700);
    analogWrite(13, 700);
    headingMag(rateFake, attitudeFake, degree , 0.0); 
    if( magOffsetMotorCount2 < 5 && degree_[0] != degree[0] && degree_[1] != degree[1] ){
    magOffsetMotorCount2 += 1;
    degree_[1] = degree[1];
    degree_[2] = degree[2];
    Serial.print("degreeX = ");
    Serial.print(degree[1]);
    Serial.print(" degreeY = ");
    Serial.print(degree[2]);
    Serial.println();
    }else if ( magOffsetMotorCount2  == 5){
    sumMagOffsetMotor2[0] = degree[1];
    sumMagOffsetMotor2[1] = degree[2];
    analogWrite(14, 0);
    analogWrite(15, 0);
    analogWrite(12, 0);
    analogWrite(13, 0);
    break;
  }
  }
    Serial.println();
    Serial.println("ORT 2 = ");
    Serial.println();
    Serial.print("sumMagX = ");
    Serial.print(sumMagOffsetMotor2[0]);
    Serial.print(" sumMagY = ");
    Serial.print(sumMagOffsetMotor2[1]);
    Serial.println();

    magOffsetMotorEpr[0] = (sumMagOffsetMotor[0] - sumMagOffsetMotor2[0]);
    magOffsetMotorEpr[1] = (sumMagOffsetMotor[1] - sumMagOffsetMotor2[1]);

    Serial.println();
    Serial.println("LAST 2 = ");
    Serial.println();
    Serial.print(" sumMaglastY= ");
    Serial.print(magOffsetMotorEpr[0]);
    Serial.print(" sumMaglastY = ");
    Serial.print(magOffsetMotorEpr[1]);
    Serial.println();   
  


   EEPROM.write(12,highByte(int(destination2[0]*100)));
   EEPROM.write(13,lowByte(int(destination2[0]*100)));
  
   EEPROM.write(14,highByte(int(destination2[1]*100)));
   EEPROM.write(15,lowByte(int(destination2[1]*100)));

   EEPROM.write(10,highByte(magOffset[0]));
   EEPROM.write(11,lowByte(magOffset[0]));

   EEPROM.write(20,highByte(magOffset[1]));
   EEPROM.write(21,lowByte(magOffset[1]));
  
   EEPROM.write(30,highByte(magOffset[2]));
   EEPROM.write(31,lowByte(magOffset[2]));

   EEPROM.write(40,highByte(magOffsetMotorEpr[0]));
   EEPROM.write(41,lowByte(magOffsetMotorEpr[0]));

   EEPROM.write(50,highByte(magOffsetMotorEpr[1]));
   EEPROM.write(51,lowByte(magOffsetMotorEpr[1]));

     
  }

void AHRS::headingMag(float attitude_rate[3],float  input[3],float degree[4], float throttle){
  
  I2Cread(MAG_ADDRESS,0x02,1,&ST1);
  
if (ST1 & 0x01){
 uint8_t Mag[7]; 
I2Cread(MAG_ADDRESS,0x03,7,Mag);
// Create 16 bits values from 8 bits data
// Magnetometer
    mag_int[0]=(Mag[3]<<8 | Mag[2]);
    mag_int[1]=(Mag[1]<<8 | Mag[0]);
    mag_int[2]=(Mag[5]<<8 | Mag[4]); 
  
  if(input[0] < 0.1 && input[0] > -0.1 && input[1] > -0.1 && input[1] < 0.1 ){//&&  throttle == 0
  if((mag_int[2]* mRes * destination[2]) < 600){
  magOffset[2] = 600 - (mag_int[2]* mRes * destination[2]);
  }else{
  magOffset[2] = -((mag_int[2]* mRes * destination[2])-600 );
  }
}

 
    magOffsetMotorFnl2[0] =  magOffsetMotorEpr[0]*(((float)map(100*constrain(throttle,0,700),0,70000,0,100))/100); 
    magOffsetMotorFnl2[1] =  magOffsetMotorEpr[1]*(((float)map(100*constrain(throttle,0,700),0,70000,0,100))/100);


  
    mag[0] = (mag_int[0]* mRes * destination[0]) - magOffset[0] + magOffsetMotorFnl2[0];
    mag[1] = (mag_int[1]* mRes * destination[1]) - magOffset[1] + magOffsetMotorFnl2[1]; 
    mag[2] = (mag_int[2]* mRes * destination[2]) + magOffset[2]; 
    
   // mag[0] *= destination2[0];
   // mag[1] *= destination2[1];

   degree[1] =  mag[0];
   degree[2] =  mag[1];
   degree[3] =  mag[2];
   
    float roll;
    float pitch;
    
    pitch = asin(input[1]);
    roll = -asin(input[0]);

    float cosRoll = cos(roll);
    float sinRoll = sin(roll);  
    float cosPitch = cos(pitch);
    float sinPitch = sin(pitch);
  
    float Xh =  mag[0] * cosPitch +  mag[2] * sinPitch;
    float Yh =  mag[0] * sinRoll * sinPitch +  mag[1] * cosRoll -  mag[2] * sinRoll * cosPitch;
   
    float heading1 = atan2(Yh, Xh);
 
    float declinationAngle2 = (4.0 + (26.0 / 60.0)) / (180 / M_PI);

    heading1 += declinationAngle2;
    // Correct for heading < 0deg and heading > 360deg
    if(heading1 < 0) {
    heading1 += 2 * PI; }
    if(heading1 > 2 * PI){
    heading1 -= 2 * PI;}
    
    previousHeadingDegrees = headingDegrees;
    
    headingDegrees = heading1 * 180/M_PI; 

  
   unsigned long headingCurrentMillis = millis();


   if(throttle < 100){
   headingDegreesDefoult = headingDegrees;
   HeadingLoop =0;
   }

  int turnRight;
  int turnLeft ;
 
  if( HeadingCount == true){

  if(headingDegreesDefoult - previousHeadingDegrees < 30 &&  headingDegreesDefoult - previousHeadingDegrees > -30){
     errorDirection = headingDegreesDefoult - previousHeadingDegrees;
  }

    
  if( errorDirection > 0  ){
   
  if(previousHeadingDegrees - headingDegrees  < -300 || turnLeft == 1){ // 360 to 0
    HeadingLoop = -360;
    turnLeft = 1;
  }
  
  if(previousHeadingDegrees - headingDegrees  > 300 && turnLeft == 1){  // 0 to 360
    turnLeft = 0;
    HeadingLoop = 0;
  }
  }else{
    
   if( ( previousHeadingDegrees - headingDegrees  > 300 || turnRight == 1 ) ){ // 360 to 0
    HeadingLoop = 360;
    turnRight = 1;
  }
  
  if(previousHeadingDegrees - headingDegrees  < -300 && turnRight == 1){  // 0 to 360
    turnRight = 0;
    HeadingLoop = 0;
  }
    
  }
 }
  HeadingCount = true;

   degree[0] = headingDegrees  - headingDegreesDefoult + HeadingLoop ; //MEAN_GYRO
   /*
   Serial.print("  ,  ");
   Serial.print(headingDegrees);
   Serial.println(); */
   
/*
    float degree_[2];
    degree[0] = (0.85*(float)degree[0]) + ((1-0.85)*(float)degree_[0]);
    degree_[0] = degree[0];
 
*/
/*
   Serial.print(degree[0]);
   Serial.print(" , ");
   Serial.print(headingDegrees);
   Serial.print("  ,  ");
   Serial.print( errorDirection );
   Serial.print("  ,  ");
   Serial.print(previousHeadingDegrees - headingDegrees );
   Serial.print("  ,  ");
   Serial.print(HeadingLoop);
   Serial.println(); 
*/
   
   /*
   Serial.print(mag[0]);
   Serial.print(" , ");
   Serial.print(mag[1]);
   Serial.print(" , ");
   Serial.print(mag[2]);
   Serial.print("  ,  ");
   Serial.print(destination2[0]);
   Serial.print("  ,  ");
   Serial.print(magOffset[0]);
   Serial.print("  ,  ");
   Serial.print(headingDegrees); // -0.04 , 0.00 , -66  ,  389  ,  924  ,  104.06  ,  109.10
   Serial.println(); */
 /*
  Serial.print("MEAN:"); 
  Serial.print(MEAN_GYRO[0]);
  Serial.print("MEAN:");
  Serial.print(MEAN_GYRO[1]);
  Serial.print("MEAN:");
  Serial.print(MEAN_GYRO[2]); offz:-285 offX:-1829 offY:479
 
  
  
  
   Serial.print(magOffsetMotorEpr[0]);
   Serial.print(" , ");
   Serial.print(magOffsetMotorEpr[1]);
   Serial.print("  ,  ");
   Serial.print(magOffsetMotorFnl2[0]);
   Serial.print(" , ");
   Serial.print(magOffsetMotorFnl2[1]);
   Serial.print("  ,  ");
    */

/*
   Serial.print(throttle);
   Serial.print(" , ");
   Serial.print(mag[0]);
   Serial.print("  ,  ");
   Serial.print(mag[1]);
   Serial.print("  ,  ");
   Serial.print(mag[2] );
   Serial.print("  ,  ");
   Serial.print(headingDegrees); // -0.04 , 0.00 , -66  ,  389  ,  924  ,  104.06  ,  109.10
   Serial.println(); 
   
 */
  }
}
