ClockWorkKid/WiFi-Nano-Quadcopter/Tests/ESP-Quadcopter-Codes/espcopter-ROS/src/espcopter/espcopter.h

#include <EEPROM.h>
#include <Wire.h>

#include "global.h"
#include "Parameter.h"

#include "pid.h"
#include "AHRS.h"


PID oto;
PID xOpt;
PID yOpt;

PID xMulti;
PID yMulti;

PID xMultiM;
PID yMultiM;

PID xLps;
PID yLps;

PID xGOT;
PID yGOT;


AHRS ahrs;

PID roll;
PID pitch;
PID yaw;

#include "setup.h"
#include "FlightControl.h"
