ClockWorkKid/WiFi-Nano-Quadcopter/Tests/Codes-Test/SONAR/IR_Receiver/serial_IR.ino

//#include <SoftwareSerial.h>
//
//SoftwareSerial irSerial(4, 5); // RX TX
//
//void setup(){
//  Serial.begin(115200);
//  irSerial.begin(1200);
//}
//
//void loop(){
//  if (irSerial.available())
//    Serial.write(irSerial.read());
//}
