ClockWorkKid/WiFi-Nano-Quadcopter/Tests/Codes-Test/SONAR/IR_Transmitter/carrier_IR_TSOP.ino

//#define IR 12
//#define CARRIER 9
//
//void setup(){
//  pinMode(IR, OUTPUT);
//  tone(CARRIER, 38000);
//}
//void loop(){
//  digitalWrite(IR, HIGH);
//  delay(500);
//  digitalWrite(IR, LOW);
//  delay(500);
//}
